MOSH-Insa-Toulouse/2023-2024_4GP_DELCAMPO_VALENCIA/APK_GraphSense/button_BACK.webp

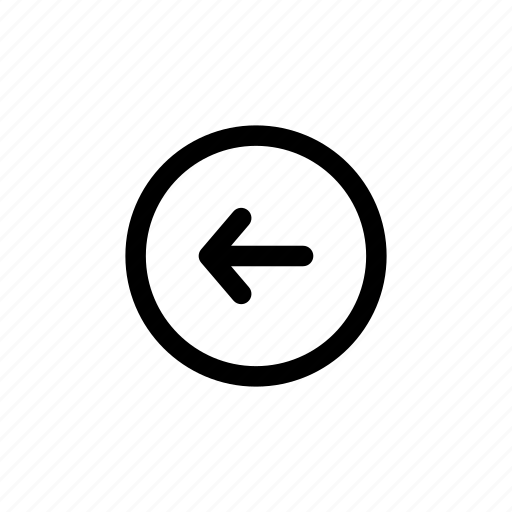
APK_GraphSense/button_BACK.webp
