MOSH-Insa-Toulouse/2023-2024_4GP_DELCAMPO_VALENCIA/ProgrammesArduino/Capteur/AmpliCapteur.asc

C1: cap; 100n
C2: cap; 100n
C3: cap; 100n
C4: cap; 1µ; V=16 Irms=0 Rser=0 Lser=0 mfg="Murata" pn="GRM155R61C105KA12" type="X5R"
C5: cap; 1p
R1: res; 100k
R2: res; 1k
R3: res; 100k
R5: res; 10k
R6: res; 1k
U1: LTC1050
V1: voltage; 5
V2: voltage; PULSE(0 1 0.2 0.1 0.1 20); AC 1
V3: voltage; SINE(0 325 50)
X1: Capteur_gaz
Named nets: 0, ADC
.tran 2
;.ac dec 100 0.1 1G
