MOSH-Insa-Toulouse/2023-2024_4GP_DELCAMPO_VALENCIA/ProgrammesArduino/Capteur/Capteur gaz.asc

B1: bi; I=V(cp,cn)*((10n+v(gc,gn)*10n))
C1: cap; 200µ
R1: res; 1k
Named nets: cp, cn, gp, gn, gc
