MOSH-Insa-Toulouse/2023-2024_4GP_DELCAMPO_VALENCIA/ProgrammesArduino/Capteur/TP3_HardwareDebouncing/TP3_HardwareDebouncing.ino

//Program by Jeremy Blum  <a href="http://www.jeremyblum.com" class="_blanktarget">www.jeremyblum.com</a>
//Debounced Switch Input via hardware

int switchPin = 2;
int ledPin = 13;
boolean lastButton = LOW;
boolean ledOn = false;
void setup()
{
  pinMode(switchPin, INPUT);
  pinMode(ledPin, OUTPUT);
  Serial.begin(9600);
}
void loop() 
{
  Serial.println(digitalRead(switchPin));
  if (digitalRead(switchPin) == HIGH && lastButton == LOW)
  {
    ledOn = !ledOn;
    lastButton = HIGH;
  }
  else
  {
    //lastButton = LOW;
    lastButton = digitalRead(switchPin);
  }
  
  digitalWrite(ledPin, ledOn);
}
