MOSH-Insa-Toulouse/2023-2024_4GP_DELCAMPO_VALENCIA/ProgrammesArduino/Capteur/Scanner_I2C/Scanner_I2C.ino

/*
   ______               _                  _///_ _           _                   _
  /   _  \             (_)                |  ___| |         | |                 (_)
  |  [_|  |__  ___  ___ _  ___  _ __      | |__ | | ___  ___| |_ _ __ ___  _ __  _  ___  _   _  ___
  |   ___/ _ \| __|| __| |/ _ \| '_ \_____|  __|| |/ _ \/  _|  _| '__/   \| '_ \| |/   \| | | |/ _ \
  |  |  | ( ) |__ ||__ | | ( ) | | | |____| |__ | |  __/| (_| |_| | | (_) | | | | | (_) | |_| |  __/
  \__|   \__,_|___||___|_|\___/|_| [_|    \____/|_|\___|\____\__\_|  \___/|_| |_|_|\__  |\__,_|\___|
                                                                                      | |
                                                                                      \_|
  Fichier :       scannerI2C.ino
  
  Description :   Scanne les 127 adresses i2c possibles, à la recherche de périphériques connectés sur l'Arduino
                  (affiche l'adresse des périphériques détectés)

  Auteur :        Jérôme TOMSKI (https://passionelectronique.fr/)
  Créé le :       25.07.2021

*/

#include <Wire.h>                         // Appel de la bibliothèque Wire.h, afin de pouvoir envoyer des commandes sur le port i2c

byte nombreDePeripheriquesTrouves = 0;    // Variable indiquant combien de périphériques ont été trouvés en scannant le port I2C

// ========================
// Initialisation programme
// ========================
void setup() {

  // Initialisation de la liaison série, côté PC (pour y faire afficher des infos, via le moniteur série de l'IDE Arduino)
  Serial.begin(9600);
  Serial.println(F("                                    ~~ SCANNER I2C ~~                                       "));
  Serial.println(F("Scanne toutes les adresses i2c, afin de repérer tous les périphériques connectés à l'arduino"));
  Serial.println(F("============================================================================================"));
  Serial.println();

  // Initialisation de la liaison i2C
  Wire.begin();

  // Boucle de parcous des 127 adresses i2c possibles
  for (byte adresseI2C = 0; adresseI2C < 127; adresseI2C++)
  {
    Wire.beginTransmission(adresseI2C);             // Interrogation de l'adresse i2c ciblée
    if (Wire.endTransmission () == 0)               // Si cela s'est bien passé, c'est qu'il y a un périphérique répondant à cette adresse
    {
      Serial.print(F("Périphérique i2c trouvé à l'adresse : "));
      Serial.print(adresseI2C, DEC);                // On affiche son adresse au format décimal
      Serial.print(F(" (0x"));
      Serial.print(adresseI2C, HEX);                // ... ainsi qu'au format héxadécimal (0x..)
      Serial.println(F(")"));
      
      nombreDePeripheriquesTrouves++;
      delay(1);                                     // Temporisation, avant de passer au scan de l'adresse suivante
    }
  }

  // Affichage final, indiquant le nombre total de périphériques trouvés sur le port I2C de l'arduino
  if (nombreDePeripheriquesTrouves == 0) {
    Serial.println(F("Aucun périphérique I2C trouvé…"));
  }
  else if (nombreDePeripheriquesTrouves == 1) {
    Serial.println();
    Serial.println(F("1 périphérique trouvé !"));
  }
  else {
    Serial.println();
    Serial.print(nombreDePeripheriquesTrouves);
    Serial.println(F("périphériques trouvés !"));
  }
  Serial.println(F("Scan terminé."));  
  
}

// =================
// Boucle principale
// =================
void loop() {
  // Aucun code ici, car tout se passe dans la fonction setup !
}
